Beaupre-Circuit-Design/c64-Pi1541/Images/Pi1541_Assembly_Rear.jpg

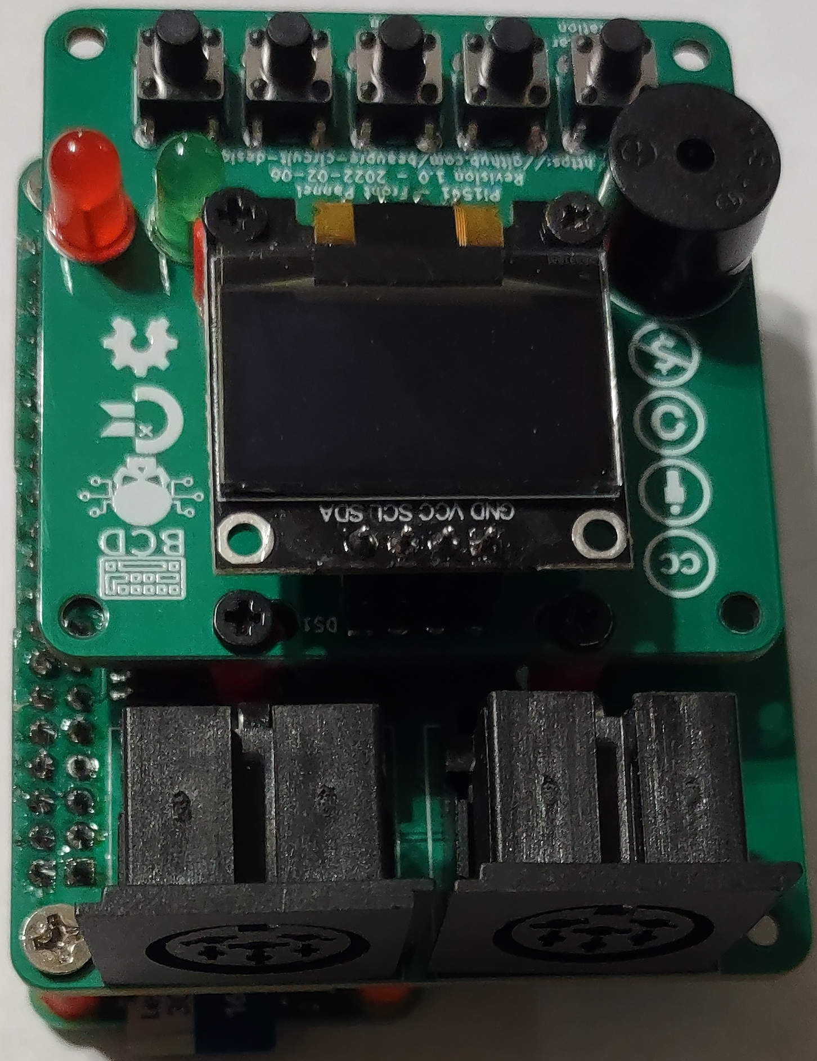
Images/Pi1541_Assembly_Rear.jpg
